BrunaMS/esp32-wifi/firmware/main/src/component/wifi.c

#include "wifi.h"

#include <string.h>
#include "freertos/FreeRTOS.h"
#include "freertos/task.h"
#include "freertos/event_groups.h"

#include "esp_system.h"
#include "esp_log.h"

#include "nvs_flash.h"
#include "lwip/err.h"
#include "lwip/sys.h"

#define TAG "Wi-Fi"

void wifiInitNvs(){
    esp_err_t ret = nvs_flash_init();
    if (ret == ESP_ERR_NVS_NO_FREE_PAGES || ret == ESP_ERR_NVS_NEW_VERSION_FOUND) {
        ESP_LOGE(TAG, "Error initializing nvs. Erasing to try again.");
        nvs_flash_erase();
        ret = nvs_flash_init();
    }
}

#ifdef CONFIG_WIFI_DEVICE_MODE_RECEIVER
void wifiInitSta(esp_event_handler_t handler)
{
    wifiInitNvs();

    esp_netif_init();
    esp_event_loop_create_default();
    esp_netif_create_default_wifi_sta();

    wifi_init_config_t cfg = WIFI_INIT_CONFIG_DEFAULT();
    esp_wifi_init(&cfg);

    esp_event_handler_instance_t instance_any_id;
    esp_event_handler_instance_t instance_got_ip;
    esp_event_handler_instance_register(WIFI_EVENT,
                                        ESP_EVENT_ANY_ID,
                                        handler,
                                        NULL,
                                        &instance_any_id);
                                        
    esp_event_handler_instance_register(IP_EVENT,
                                        IP_EVENT_STA_GOT_IP,
                                        handler,
                                        NULL,
                                        &instance_got_ip);

    wifi_config_t wifi_config = {
        .sta = {
            .ssid = ESP_WIFI_SSID,
            .password = ESP_WIFI_PASS,
            /* Authmode threshold resets to WPA2 as default if password matches WPA2 standards (pasword len => 8).
             * If you want to connect the device to deprecated WEP/WPA networks, Please set the threshold value
             * to WIFI_AUTH_WEP/WIFI_AUTH_WPA_PSK and set the password with length and format matching to
	     * WIFI_AUTH_WEP/WIFI_AUTH_WPA_PSK standards.
             */
            .threshold.authmode = ESP_WIFI_SCAN_AUTH_MODE_THRESHOLD,
            // .sae_pwe_h2e = WPA3_SAE_PWE_BOTH,
        },
    };
    esp_wifi_set_mode(WIFI_MODE_STA);
    esp_wifi_set_config(WIFI_IF_STA, &wifi_config);
    esp_wifi_start();

    ESP_LOGI(TAG, "wifi_init_sta finished.");
}
#endif

#ifdef CONFIG_WIFI_DEVICE_MODE_TRANSMITTER
void wifiInitSoftap(esp_event_handler_t handler)
{
    wifiInitNvs();
    esp_netif_init();
    esp_event_loop_create_default();
    esp_netif_create_default_wifi_ap();

    wifi_init_config_t cfg = WIFI_INIT_CONFIG_DEFAULT();
    esp_wifi_init(&cfg);

    esp_event_handler_instance_register(WIFI_EVENT,
                                        ESP_EVENT_ANY_ID,
                                        handler,
                                        NULL,
                                        NULL);

    wifi_config_t wifi_config = {
        .ap = {
            .ssid = ESP_WIFI_SSID,
            .ssid_len = strlen(ESP_WIFI_SSID),
            .channel = ESP_WIFI_CHANNEL,
            .max_connection = MAX_STA_CONN,
            .password = ESP_WIFI_PASS,
            .authmode = WIFI_AUTH_WPA_WPA2_PSK,
        },
    };
    if (strlen(ESP_WIFI_PASS) == 0) {
        wifi_config.ap.authmode = WIFI_AUTH_OPEN;
    }

    esp_wifi_set_mode(WIFI_MODE_AP);
    esp_wifi_set_config(WIFI_IF_AP, &wifi_config);
    esp_wifi_start();

    ESP_LOGI(TAG, "wifi_init_softap finished. SSID:%s password:%s channel:%d",
             ESP_WIFI_SSID, ESP_WIFI_PASS, ESP_WIFI_CHANNEL);
}
#endif
