BrunaMS/esp32-wifi/firmware/main/receiver.c

#include "freertos/FreeRTOS.h"
#include "freertos/event_groups.h"
#include "esp_log.h"
#include "wifiDriver.h"

void app_main(void)
{
    TaskHandle_t wifiHandle = NULL;

    xTaskCreate(wifiService, "wifiService", 5000, NULL, configMAX_PRIORITIES - 1, &wifiHandle);
    vTaskDelay(pdMS_TO_TICKS(5));
    vTaskDelete(NULL);
}
